alastair-duncan/SuperEZGraver/src/microPython/test1.py

#
# First test using microPython
#

import machine
import time
from machine import Pin, PWM, ADC

pulseLength = 10     # ms
maxFreq = 5000/60   # Hz - representation is Strokes Per Minute
maxADCdeflection = 1024  # depends on the board
outputPin = 0
speedPin = 1
powerPin = 2
speedBias = 20  # ignore any readings below this and don't switch on
pwmFreq = 1000  # max 1000
# configure PWM output pin
#  Duty cycle is 0..1023
pwmPin = PWM(Pin(outputPin))
pwmPin.freq(pwmFreq)

# configure input pin for analogue input - speed
# NB needs to be 0..1.0VDC?
# read() method returns 0..1024 - check this, really not 1023?
# ESP32 docs claim 0..4095; attenuation available; 12 bit resolution
# ESP8266 says 0..1024, no attenuation mentioned; 10 bit resolution
# Pi Pico 0..4095; 12 bit resolution, 0..3V3

speedSetting = ADC(speedPin)

# configure input pin for analogue input - PWM duty cycle (power)
powerSetting = ADC(powerPin)

# loop
while (True):

    # Read speed analogue input, quantise
    # Low resistance = high Voltage, high speed
    currentSpeed = maxADCdeflection - speedSetting.read()
    # Read power input
    currentPower = maxADCdeflection - powerSetting.read()  # Low resistance = high power

    if (currentSpeed >= speedBias):
        # set PWM output level on
        pwmPin.duty(currentPower)
        # Pulse length dictates duty cycle, determine minimum possible.
        # For max speed of 5000SPM can't go above 6ms and manage 50% duty cycle (assuming max power)
        time.sleep_ms(pulseLength)
        # Set output low - off time
        pwmPin.duty(0)

        # ms  Note that without the bias setting we're into divide-by-zero territory
        quantisedPeriod = 1/(maxFreq * currentSpeed/maxADCdeflection) * 1000
        time.sleep_ms(quantisedPeriod - pulseLength)
    else:
        time.sleep_ms(100)  # Because why not
